JakubFranek/Home-Air-Monitoring-System/docs/images/HAMS_hub_nodes.JPG

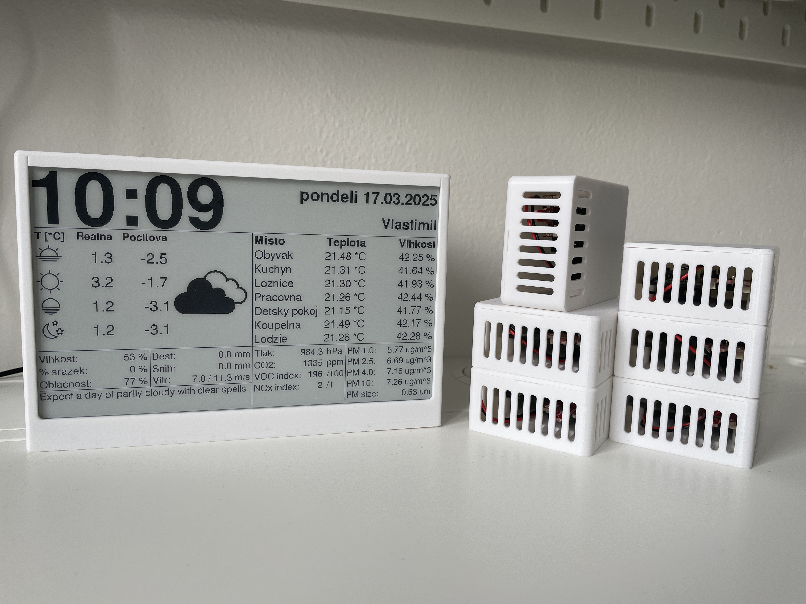
docs/images/HAMS_hub_nodes.JPG
