JakubFranek/Home-Air-Monitoring-System/docs/images/HAMS_node_board_battery.JPG

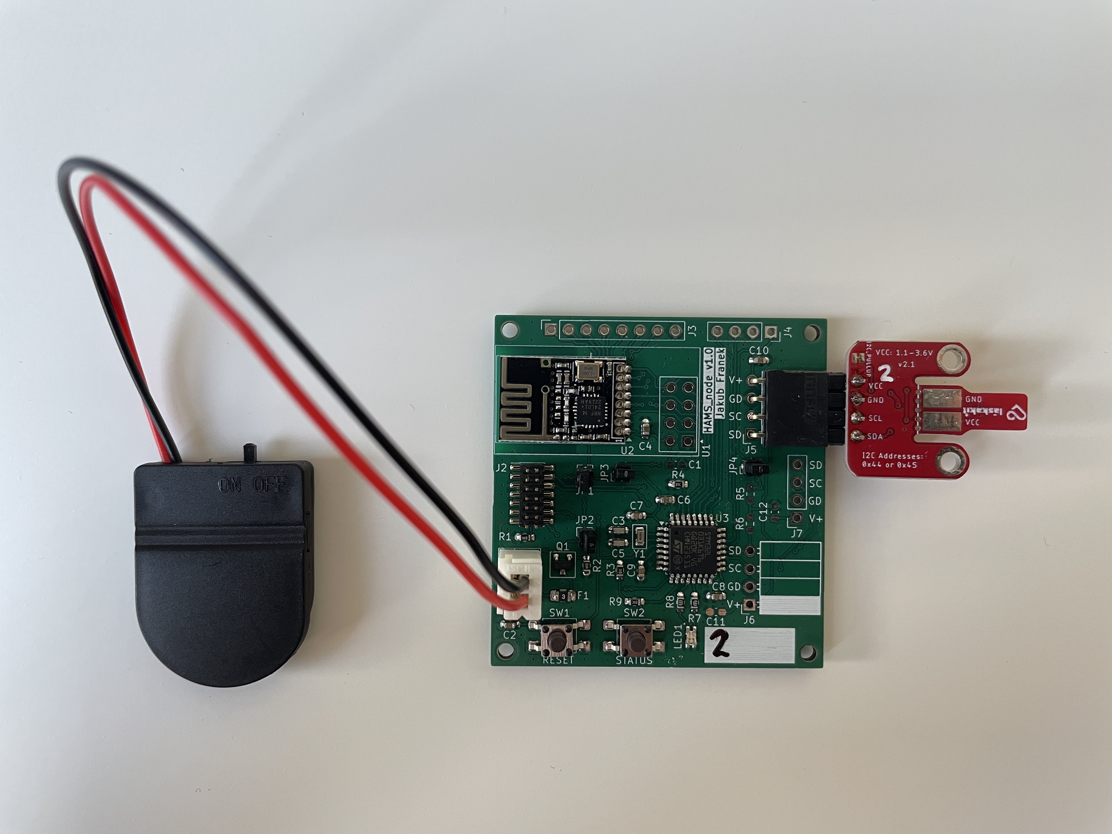
docs/images/HAMS_node_board_battery.JPG
