JakubFranek/Home-Air-Monitoring-System/hub/firmware/resources/images/weather/01d_bw.png

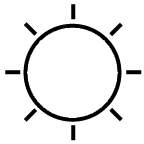
hub/firmware/resources/images/weather/01d_bw.png
