JakubFranek/Home-Air-Monitoring-System/hub/firmware/resources/images/weather/02d_bw.png

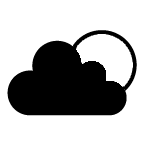
hub/firmware/resources/images/weather/02d_bw.png
