JakubFranek/Home-Air-Monitoring-System/hub/firmware/resources/images/weather/04d_bw.png

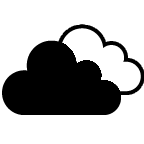
hub/firmware/resources/images/weather/04d_bw.png
