JakubFranek/Home-Air-Monitoring-System/hub/firmware/resources/images/weather/09d_bw.png

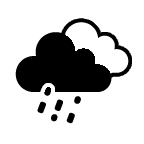
hub/firmware/resources/images/weather/09d_bw.png
