JakubFranek/Home-Air-Monitoring-System/hub/firmware/resources/images/weather/10d_bw.png

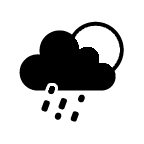
hub/firmware/resources/images/weather/10d_bw.png
