JakubFranek/Home-Air-Monitoring-System/hub/firmware/resources/images/weather/11d_bw.png

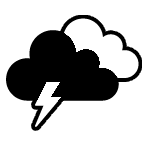
hub/firmware/resources/images/weather/11d_bw.png
