JakubFranek/Home-Air-Monitoring-System/hub/firmware/resources/images/weather/13d_alt_bw.png

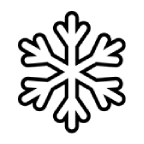
hub/firmware/resources/images/weather/13d_alt_bw.png
