JakubFranek/Home-Air-Monitoring-System/hub/firmware/resources/images/weather/50d_bw.png

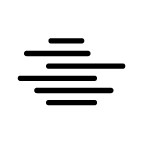
hub/firmware/resources/images/weather/50d_bw.png
