JakubFranek/Home-Air-Monitoring-System/hub/firmware/main/weather_icons.h

#include <stdint.h>

/*
 * Byte arrays generated using https://javl.github.io/image2cpp/

 * Byte array names are:
 * weather_01d, weather_02d, weather_03d, weather_04d, weather_09d, weather_10d, weather_11d, weather_13d, weather_50d
 *
 * All byte arrays are 144x144 px, this is because it is the smallest dimension for the orginial openweathermap
 * images to not be clipped, which leads to number of pixels divisible by 8:
 * 144 px * 144 px / 8 = 20736 px / 8 = 2592 bytes per picture
 */

#define WEATHER_ICON_SIZE 144                                          // px
#define WEATHER_ICON_BYTES (WEATHER_ICON_SIZE * WEATHER_ICON_SIZE) / 8 // bytes

const uint8_t weather_01d[WEATHER_ICON_BYTES] = { // '01d_bw', 144x144px
    0x00, 0x00, 0x00, 0x00, 0x00, 0x00, 0x00, 0x00, 0x00, 0x00, 0x00, 0x00, 0x00, 0x00, 0x00, 0x00,
    0x00, 0x00, 0x00, 0x00, 0x00, 0x00, 0x00, 0x00, 0x00, 0x00, 0x00, 0x00, 0x00, 0x00, 0x00, 0x00,
    0x00, 0x00, 0x00, 0x00, 0x00, 0x00, 0x00, 0x00, 0x00, 0x00, 0x00, 0x00, 0x00, 0x00, 0x00, 0x00,
    0x00, 0x00, 0x00, 0x00, 0x00, 0x00, 0x00, 0x00, 0x00, 0x00, 0x00, 0x00, 0x00, 0x00, 0x00, 0x00,
    0x00, 0x00, 0x00, 0x00, 0x00, 0x00, 0x00, 0x00, 0x00, 0x00, 0x00, 0x00, 0x00, 0x00, 0x00, 0x00,
    0x01, 0xe0, 0x00, 0x00, 0x00, 0x00, 0x00, 0x00, 0x00, 0x00, 0x00, 0x00, 0x00, 0x00, 0x00, 0x00,
    0x00, 0x00, 0x01, 0xe0, 0x00, 0x00, 0x00, 0x00, 0x00, 0x00, 0x00, 0x00, 0x00, 0x00, 0x00, 0x00,
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
    0x00, 0x00, 0x00, 0x00, 0x00, 0x00, 0x00, 0x00, 0x00, 0x00, 0x00, 0x00, 0x00, 0x00, 0x00, 0x00,
    0x00, 0x00, 0x00, 0x00, 0x00, 0x00, 0x00, 0x00, 0x00, 0x00, 0x00, 0x00, 0x00, 0x00, 0x00, 0x00,
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
