JakubFranek/Home-Air-Monitoring-System/hub/firmware/main/time_of_day_icons.h

#include <stdint.h>

/*
 * Byte arrays generated using https://javl.github.io/image2cpp/

 * Byte array names are:
 * morning, day, evening, night
 *
 * All byte arrays are 48x48 px.
 * 48 px * 48 px / 8 = 2304 px / 8 = 288 bytes per picture
 */

#define TIME_OF_DAY_ICON_SIZE 48                                                   // px
#define TIME_OF_DAY_ICON_BYTES (TIME_OF_DAY_ICON_SIZE * TIME_OF_DAY_ICON_SIZE) / 8 // bytes

const uint8_t morning[TIME_OF_DAY_ICON_BYTES] = { // 'morning', 48x48px
    0x00, 0x00, 0x00, 0x00, 0x00, 0x00, 0x00, 0x00, 0x01, 0x80, 0x00, 0x00, 0x00, 0x00, 0x01, 0x80,
    0x00, 0x00, 0x00, 0x00, 0x01, 0x80, 0x00, 0x00, 0x00, 0x00, 0x01, 0x80, 0x00, 0x00, 0x00, 0x00,
    0x01, 0x80, 0x00, 0x00, 0x00, 0x00, 0x01, 0x80, 0x00, 0x00, 0x00, 0x80, 0x00, 0x00, 0x01, 0x00,
    0x01, 0xc0, 0x0f, 0xf0, 0x03, 0x80, 0x00, 0xe0, 0x7f, 0xfe, 0x07, 0x00, 0x00, 0x70, 0xf0, 0x0f,
    0x0e, 0x00, 0x00, 0x33, 0xc0, 0x03, 0xcc, 0x00, 0x00, 0x07, 0x00, 0x00, 0xe0, 0x00, 0x00, 0x0e,
    0x00, 0x00, 0x70, 0x00, 0x00, 0x1c, 0x00, 0x00, 0x38, 0x00, 0x00, 0x18, 0x00, 0x00, 0x18, 0x00,
    0x00, 0x30, 0x00, 0x00, 0x0c, 0x00, 0x00, 0x70, 0x00, 0x00, 0x0e, 0x00, 0x00, 0x60, 0x00, 0x00,
    0x06, 0x00, 0x00, 0x60, 0x00, 0x00, 0x06, 0x00, 0x00, 0xc0, 0x00, 0x00, 0x03, 0x00, 0x00, 0xc0,
    0x00, 0x00, 0x03, 0x00, 0x00, 0xc0, 0x00, 0x00, 0x03, 0x00, 0x7f, 0xff, 0xff, 0xff, 0xff, 0xfe,
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
    0x00, 0x00, 0x00, 0x00, 0x00, 0x00, 0x00, 0x00, 0x00, 0x00, 0x00, 0x00, 0x00, 0x00, 0x00, 0x00,
    0x00, 0x00, 0x00, 0x00, 0x00, 0x00, 0x00, 0x00, 0x00, 0x00, 0x00, 0x00, 0x00, 0x00, 0x00, 0x00};
