JakubFranek/Home-Air-Monitoring-System/node/firmware/STM32L031K6/Core/Inc/gpio_custom.h

#ifndef INC_GPIO_CUSTOM_H_
#define INC_GPIO_CUSTOM_H_

void nrf24l01p_set_cs(uint8_t state);
void nrf24l01p_set_ce(uint8_t state);
void set_pins_to_analog_mode(GPIO_TypeDef* port, uint32_t pins);
void reinitialize_gpio(void);

#endif /* INC_GPIO_CUSTOM_H_ */
