JakubFranek/Home-Air-Monitoring-System/hub/firmware/main/svatky_api.h

#ifdef __cplusplus
extern "C"
{
#endif

#ifndef __SVATKY_API_H__
#define __SVATKY_API_H__

#include "calendar_data.h"

    int8_t request_calendar_data(CalendarData *data);

#endif /* __SVATKY_API_H__ */

#ifdef __cplusplus
}
#endif
